Amd-Sulaiman/NFC-TEMP_SENS/nfc-temperature-logger-firmware/include/secrets.h

#pragma once

// ---- Wi-Fi credentials ----
#define WIFI_SSID     "YOUR_WIFI_SSID"
#define WIFI_PASSWORD "YOUR_WIFI_PASSWORD"

// ---- Cloud endpoint ----
// Example: https://api.example.com/ingest
#define CLOUD_URL     "https://your.server/ingest"

// Optional: bearer/API token (leave empty if not used)
#define CLOUD_AUTH_BEARER ""

// ---- Patient / device metadata ----
#define DEFAULT_PATIENT_ID "patient-001"
#define DEVICE_NAME        "esp32-c6-mini"
